0nonymous/Breadboard-CPU-Computer-System/diagrams/1.jpg

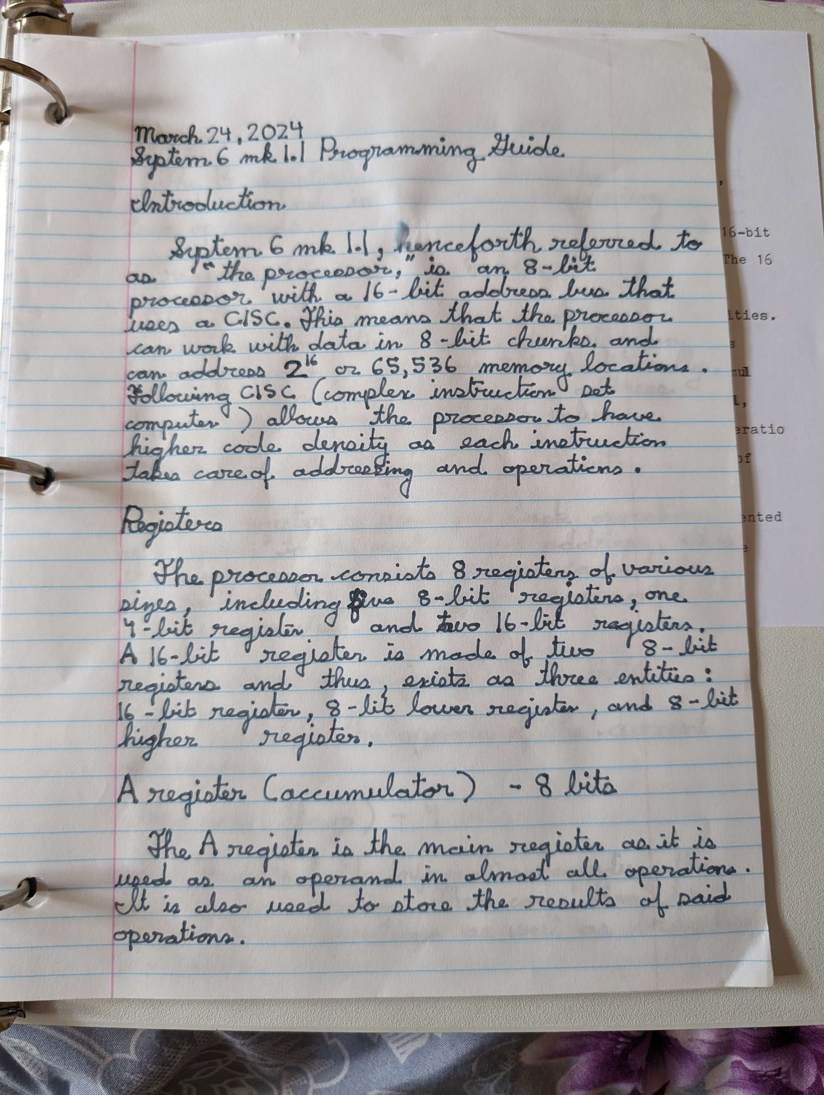
diagrams/1.jpg
