0nonymous/Breadboard-CPU-Computer-System/diagrams/2.jpg

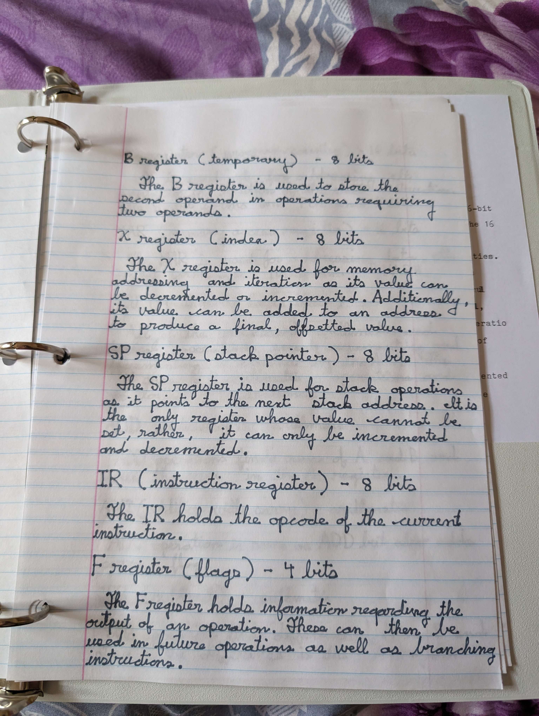
diagrams/2.jpg
