0nonymous/Breadboard-CPU-Computer-System/diagrams/3.jpg

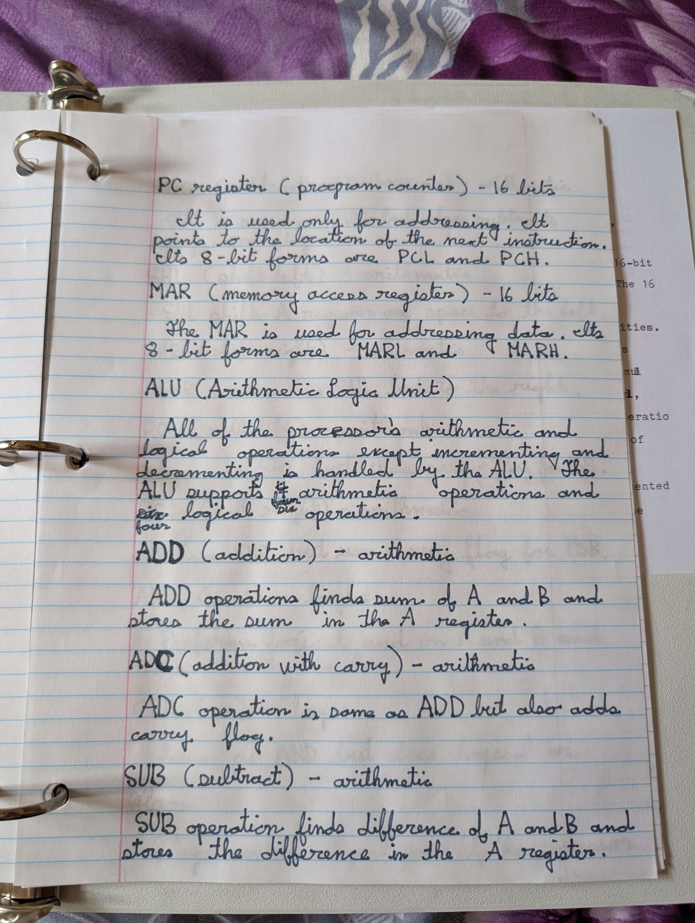
diagrams/3.jpg
