0nonymous/Breadboard-CPU-Computer-System/diagrams/4.jpg

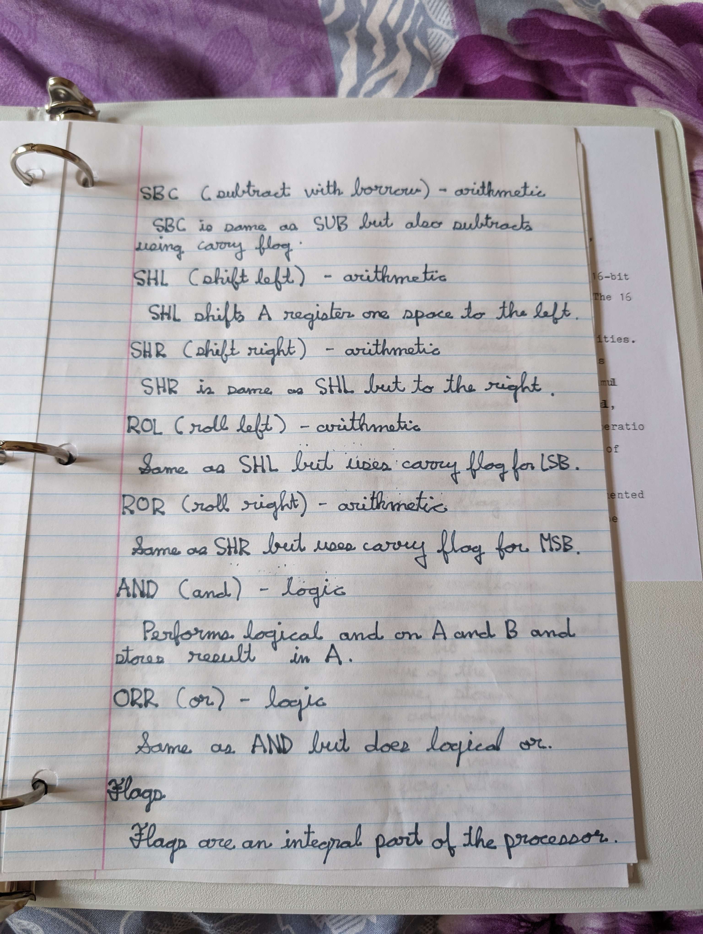
diagrams/4.jpg
