0nonymous/Breadboard-CPU-Computer-System/diagrams/5.jpg

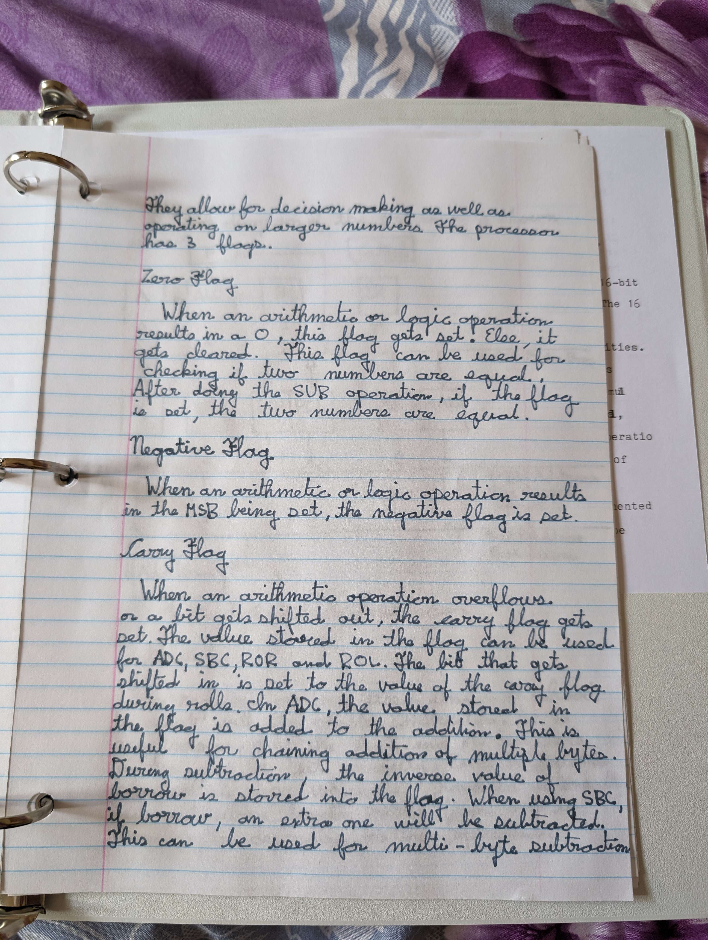
diagrams/5.jpg
