0nonymous/Breadboard-CPU-Computer-System/diagrams/6.jpg

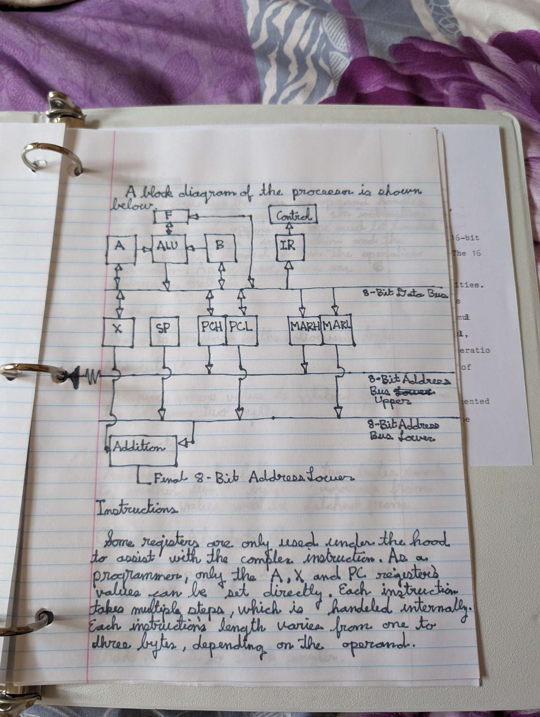
diagrams/6.jpg
