0nonymous/Breadboard-CPU-Computer-System/diagrams/7.jpg

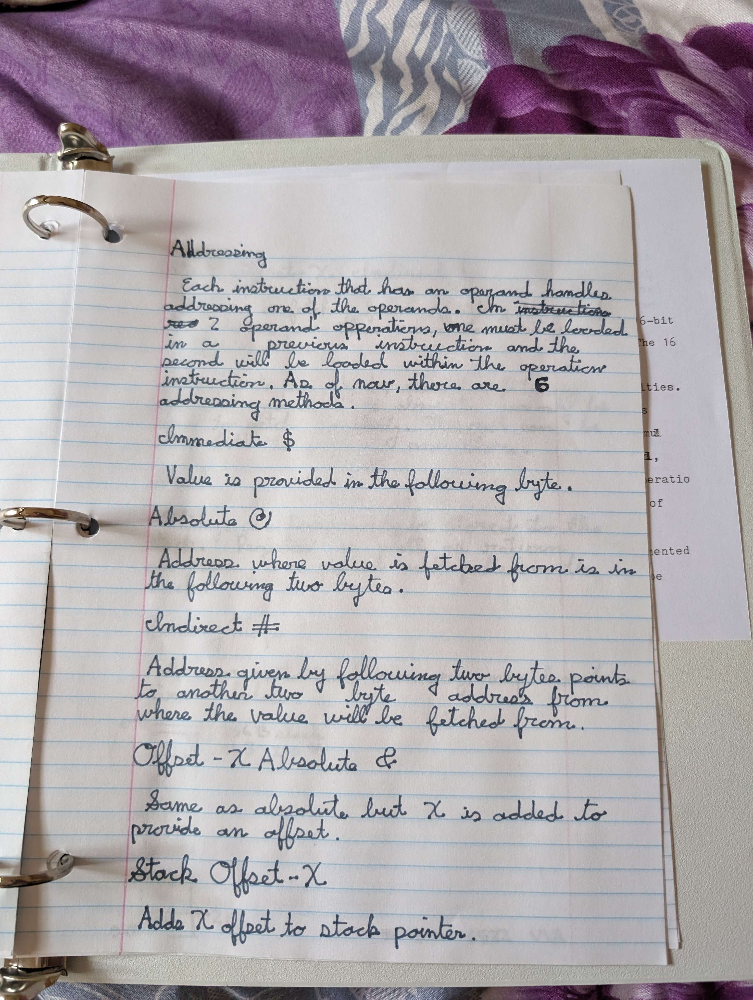
diagrams/7.jpg
