0nonymous/Breadboard-CPU-Computer-System/diagrams/8.jpg

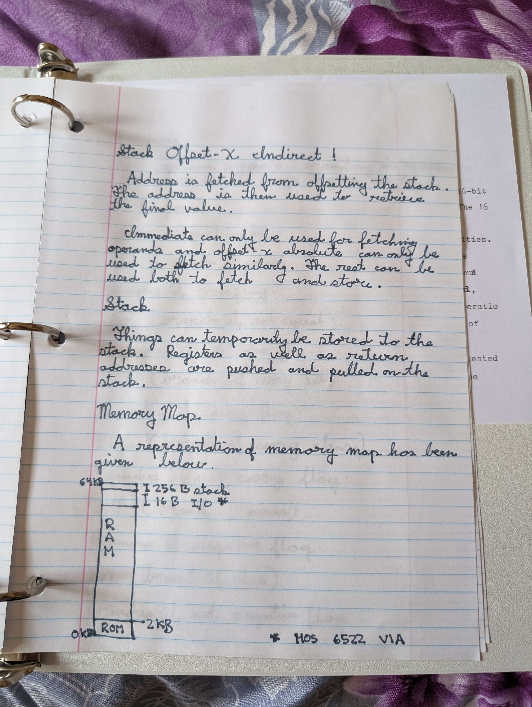
diagrams/8.jpg
