0nonymous/Breadboard-CPU-Computer-System/diagrams/9.jpg

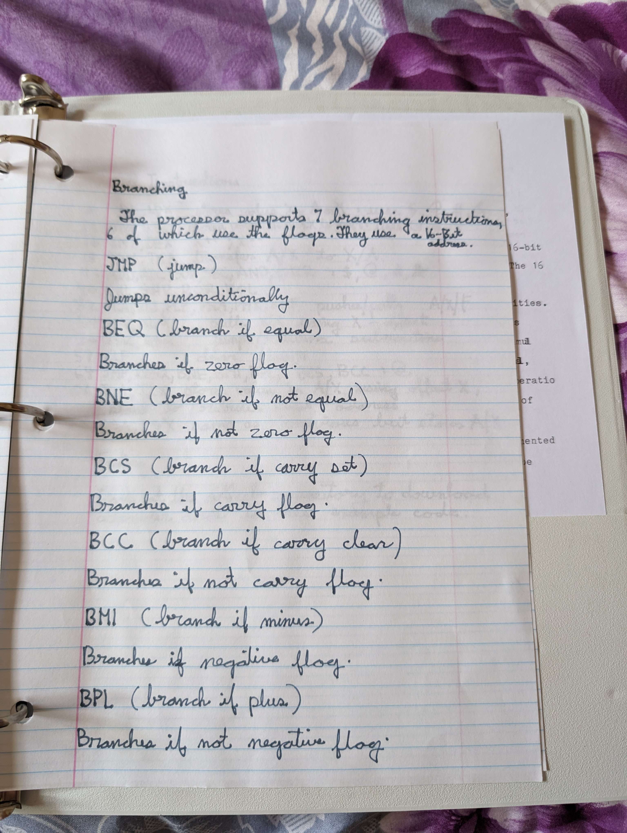
diagrams/9.jpg
