0nonymous/Breadboard-CPU-Computer-System/diagrams/10.jpg

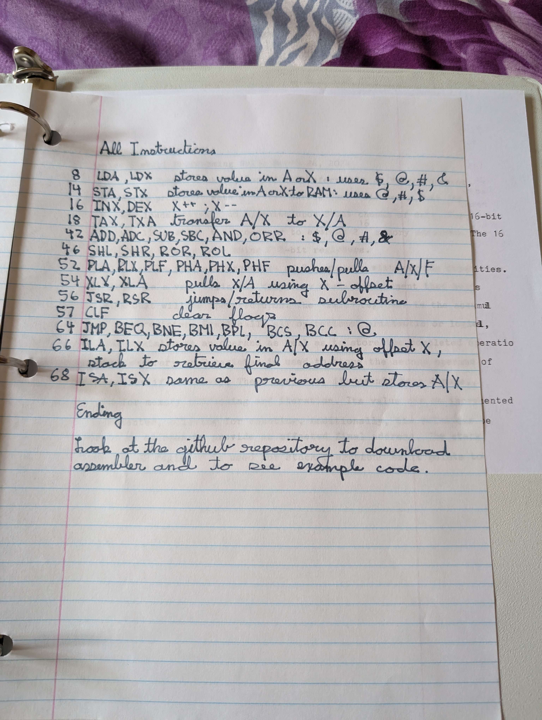
diagrams/10.jpg
