0nonymous/Breadboard-CPU-Computer-System/diagrams/IMG_1920.JPG

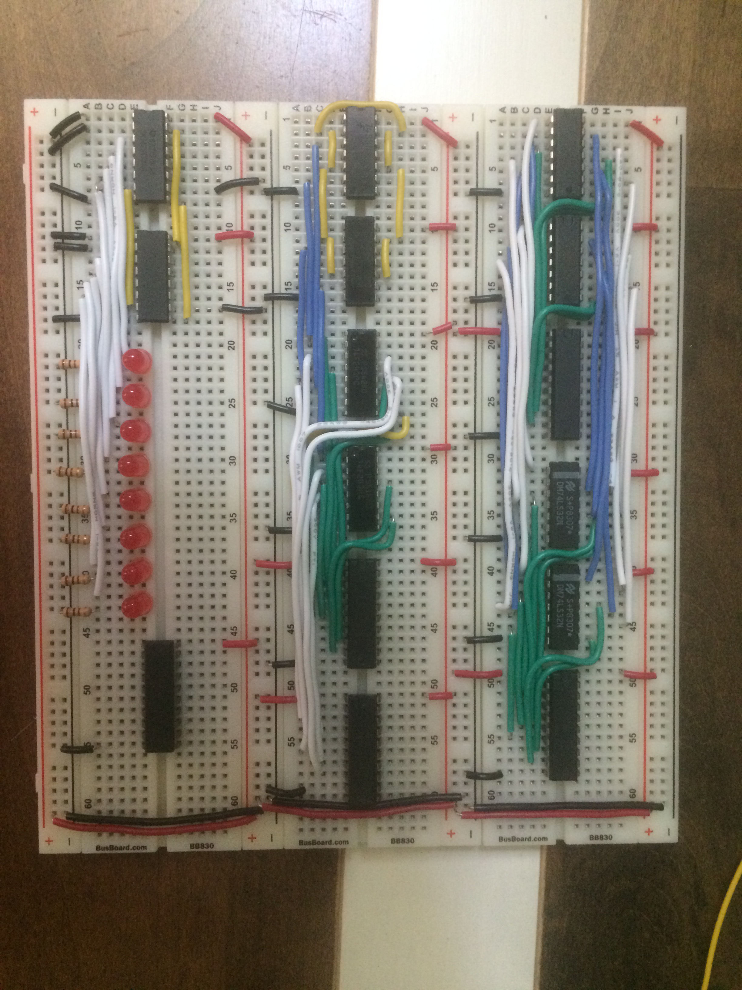
diagrams/IMG_1920.JPG
