0nonymous/Breadboard-CPU-Computer-System/diagrams/IMG_1921.JPG

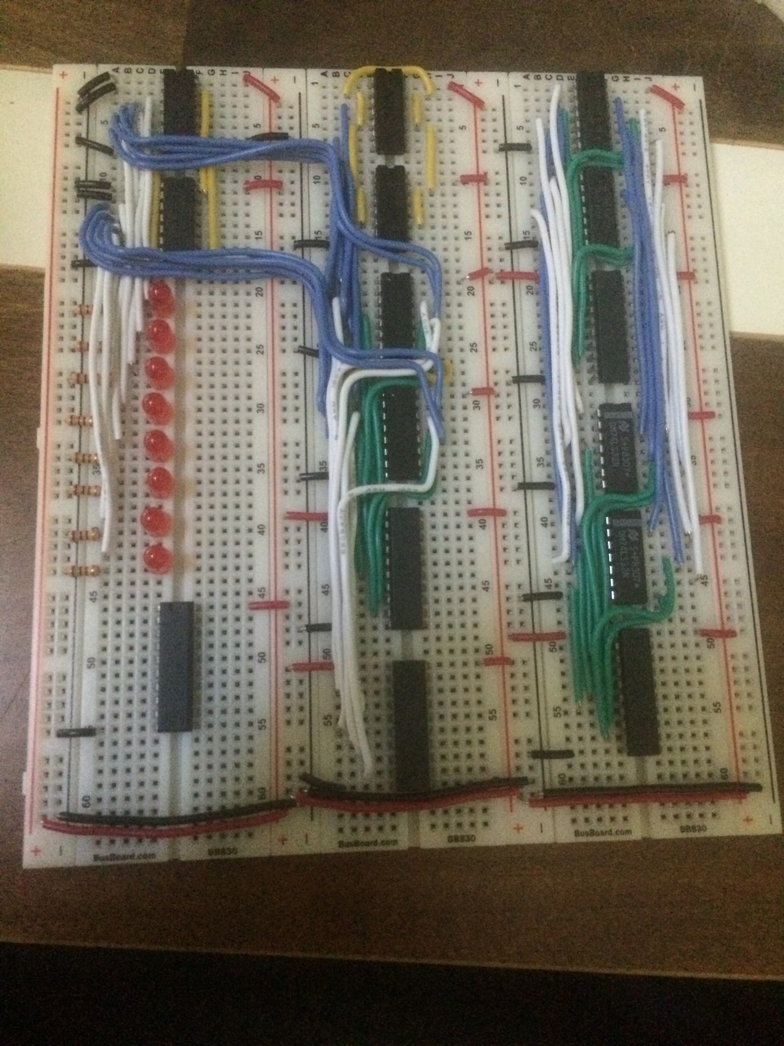
diagrams/IMG_1921.JPG
